iplayfast/cad-mouse-mk2/firmware/include/controllers/HIDController.h

#pragma once

#include <Adafruit_TinyUSB.h>
#include <Arduino.h>

class HIDController {
 public:
  void begin();
  void task();
  bool sendReports(const float motion[6], uint16_t buttonBits);

  // Called from IdleState each loop: updates the feature report buffer
  void setSensorDelta(const float delta[9]);

  // Returns true if a new calibration matrix arrived via output report.
  // Clears the flag; caller should save + apply the matrix.
  bool takeCalibrationMatrix(float matrix[6][9]);

 private:
  struct __attribute__((packed)) ReportAxes {
    int16_t x, y, z, rx, ry, rz;
  };

  struct __attribute__((packed)) ReportButtons {
    uint16_t bits;
  };

  static ReportAxes makeAxesReport(const float motion[6]);
  bool axesReportChanged(const ReportAxes& axes) const;

  // TinyUSB callback stubs — route to singleton instance
  static uint16_t onGetReport(uint8_t report_id, hid_report_type_t report_type,
                               uint8_t* buffer, uint16_t reqlen);
  static void onSetReport(uint8_t report_id, hid_report_type_t report_type,
                           uint8_t const* buffer, uint16_t bufsize);

  uint16_t handleGetReport(uint8_t report_id, uint8_t* buffer, uint16_t reqlen);
  void handleSetReport(uint8_t report_id, uint8_t const* buffer, uint16_t bufsize);

  Adafruit_USBD_HID usbHid_;
  uint16_t buttonBitsSent_ = 0;
  ReportAxes lastSentAxes_{};

  // Feature report ID 4: 9 sensor-delta floats (36 bytes)
  float sensorDelta_[9] = {};

  // Output report ID 5: pending calibration matrix (54 floats = 216 bytes)
  float pendingMatrix_[6][9] = {};
  bool calibrationMatrixReady_ = false;
};
